salkinium/textile_display/connection/matrix/matrix_1x1.dxf

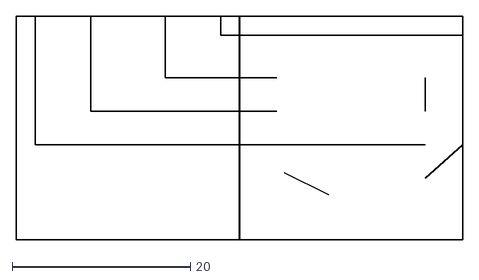
[picture p15: CAD file, 2012-10-11]
connection/matrix/matrix_1x1.dxf
50.0 x 25.0
