salkinium/textile_display/connection/matrix/matrix_3x3.dxf

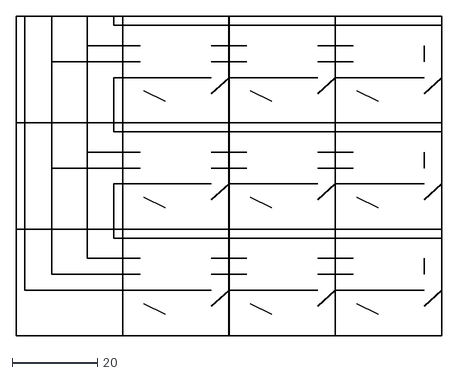
[picture p16: CAD file, 2012-10-11]
connection/matrix/matrix_3x3.dxf
100.0 x 75.0
